tjeffree/Nova75-Keyboard/marbastlib-main/3d/CON_SM13B-SRSS-TB.step

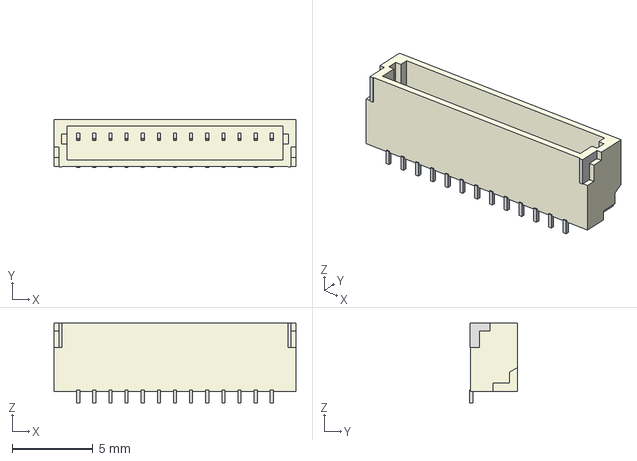
[picture p22: CAD file, 2022-10-29]
marbastlib-main/3d/CON_SM13B-SRSS-TB.step
15.0 x 2.96 x 4.95 mm
