tjeffree/Nova75-Keyboard/marbastlib-main/3d/LED_WS2812B-MINI.step

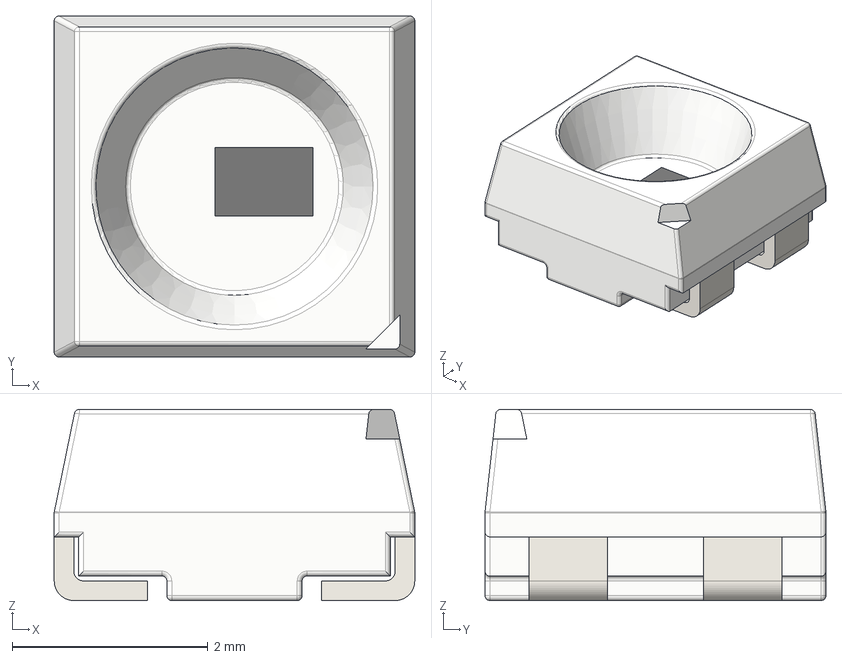
[picture p23: CAD file, 2022-10-29]
marbastlib-main/3d/LED_WS2812B-MINI.step
3.68 x 3.48 x 1.95 mm
