tjeffree/Nova75-Keyboard/marbastlib-main/3d/CON_SM08B-SRSS-TB.step

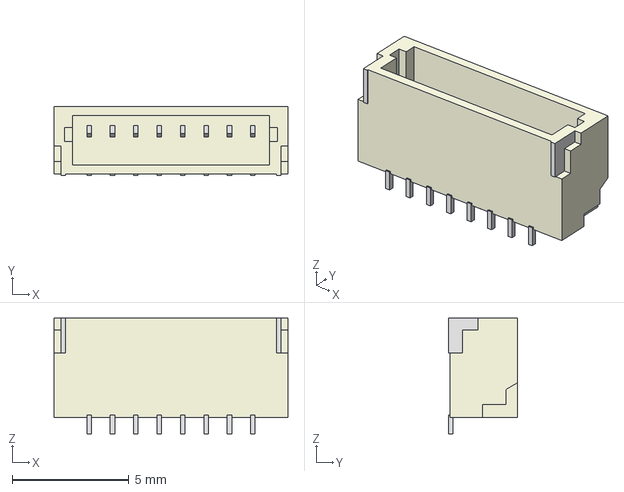
[picture p24: CAD file, 2022-10-29]
marbastlib-main/3d/CON_SM08B-SRSS-TB.step
10.0 x 2.96 x 4.95 mm
