tjeffree/Nova75-Keyboard/marbastlib-main/3d/SW_SSSS223900.step

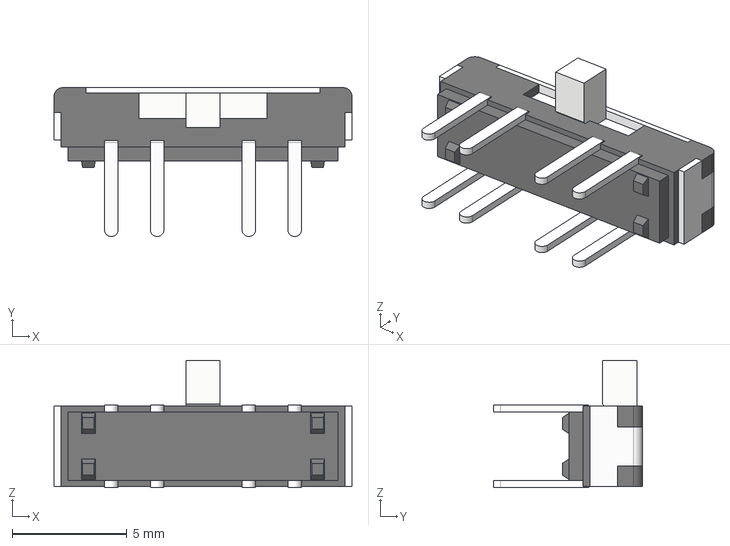
[picture p25: CAD file, 2022-10-29]
marbastlib-main/3d/SW_SSSS223900.step
13.0 x 6.50 x 5.55 mm
