tjeffree/Nova75-Keyboard/marbastlib-main/3d/CON_SM06B-SRSS-TB.step

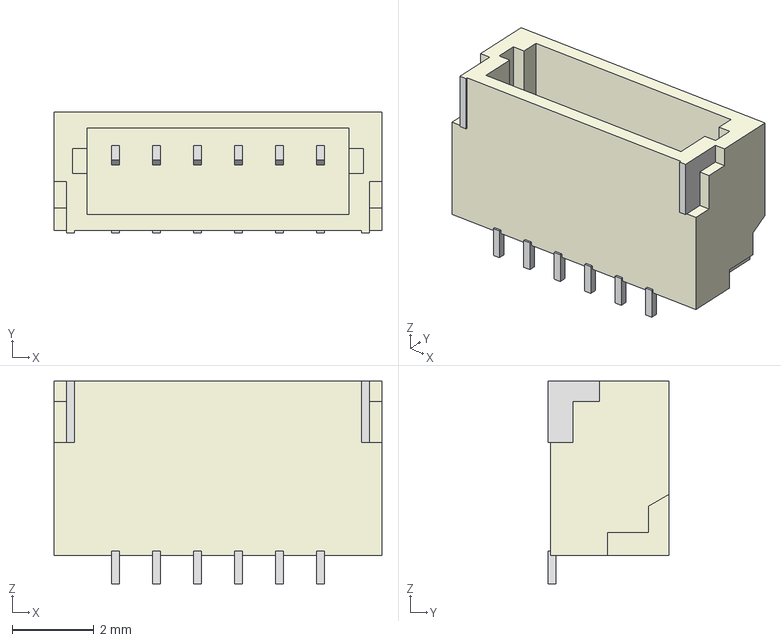
[picture p26: CAD file, 2022-10-29]
marbastlib-main/3d/CON_SM06B-SRSS-TB.step
8.00 x 2.96 x 4.95 mm
