tjeffree/Nova75-Keyboard/marbastlib-main/3d/Switch_MSK12C02.step

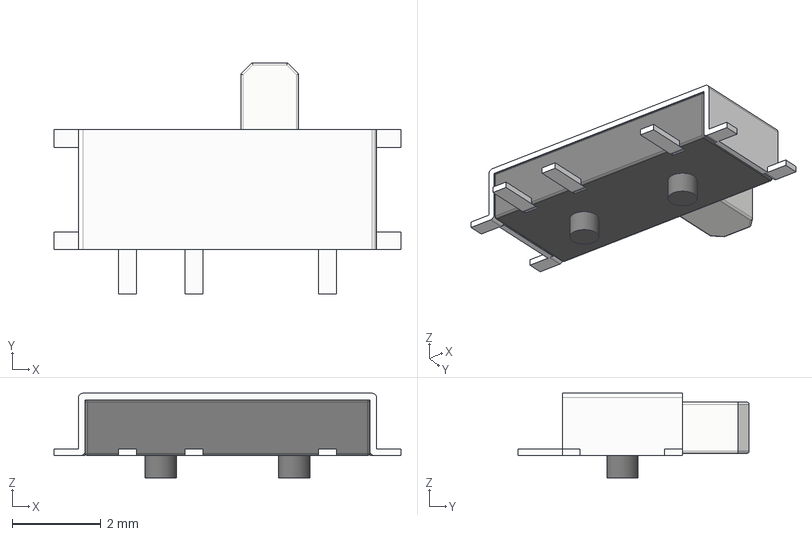
[picture p27: CAD file, 2022-10-29]
marbastlib-main/3d/Switch_MSK12C02.step
7.80 x 5.20 x 1.90 mm
