tjeffree/Nova75-Keyboard/marbastlib-main/3d/LED_WS2812_2020.step

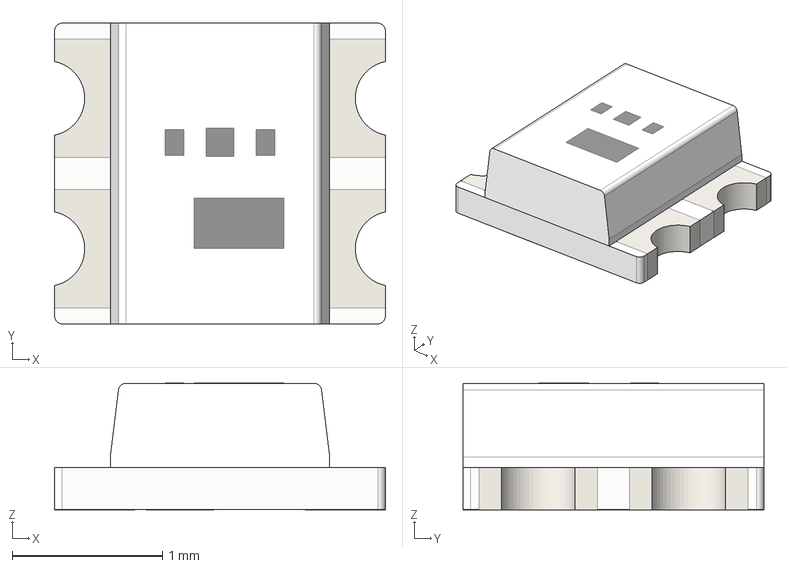
[picture p28: CAD file, 2022-10-29]
marbastlib-main/3d/LED_WS2812_2020.step
2.20 x 2.00 x 0.842 mm
