tjeffree/Nova75-Keyboard/marbastlib-main/3d/ROT_EC11E.step

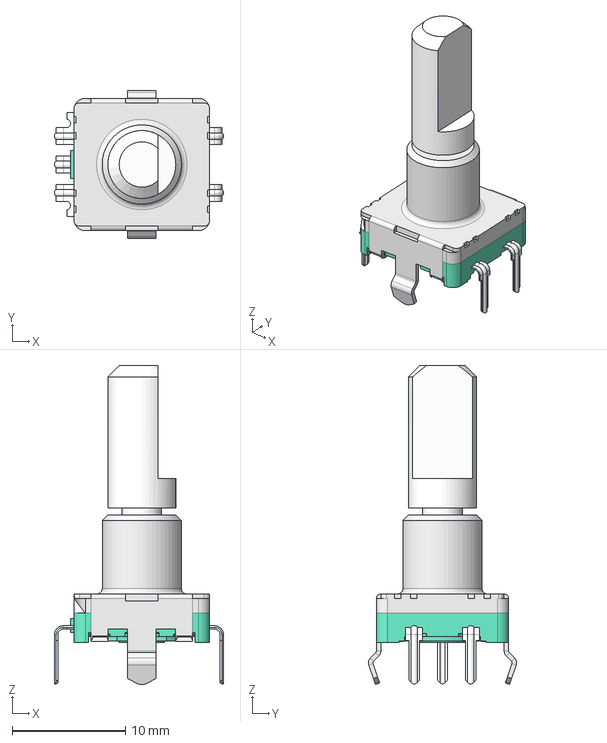
[picture p29: CAD file, 2022-10-29]
marbastlib-main/3d/ROT_EC11E.step
14.9 x 13.1 x 28.2 mm
