tjeffree/Nova75-Keyboard/marbastlib-main/3d/SW_SSSS213100.step

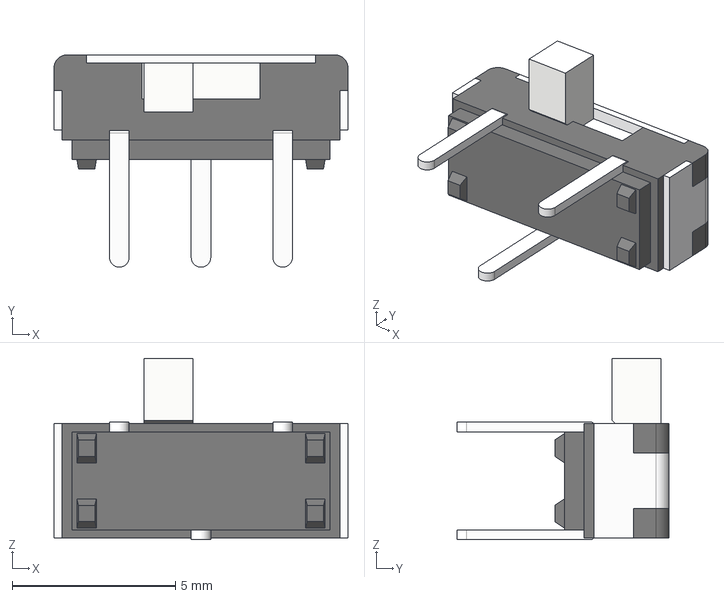
[picture p30: CAD file, 2022-10-29]
marbastlib-main/3d/SW_SSSS213100.step
9.00 x 6.50 x 5.55 mm
