tjeffree/Nova75-Keyboard/marbastlib-main/3d/CON_TYPE-C-31-M-14.step

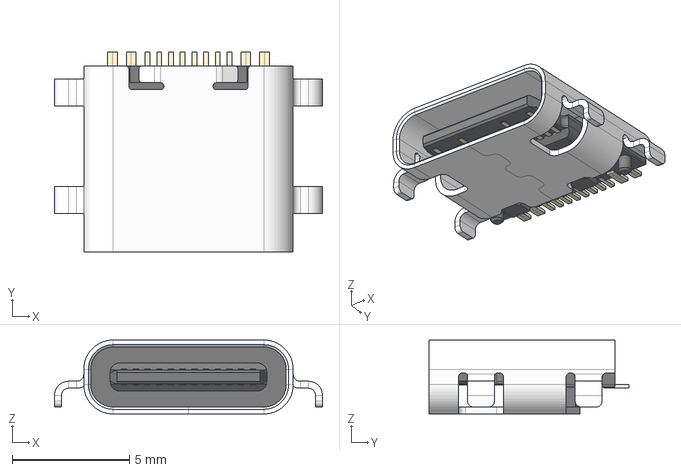
[picture p31: CAD file, 2022-10-29]
marbastlib-main/3d/CON_TYPE-C-31-M-14.step
11.5 x 8.56 x 3.16 mm
Shroud
Plastic Body & Connector
