tjeffree/Nova75-Keyboard/marbastlib-main/3d/Switch_ESP3020.step

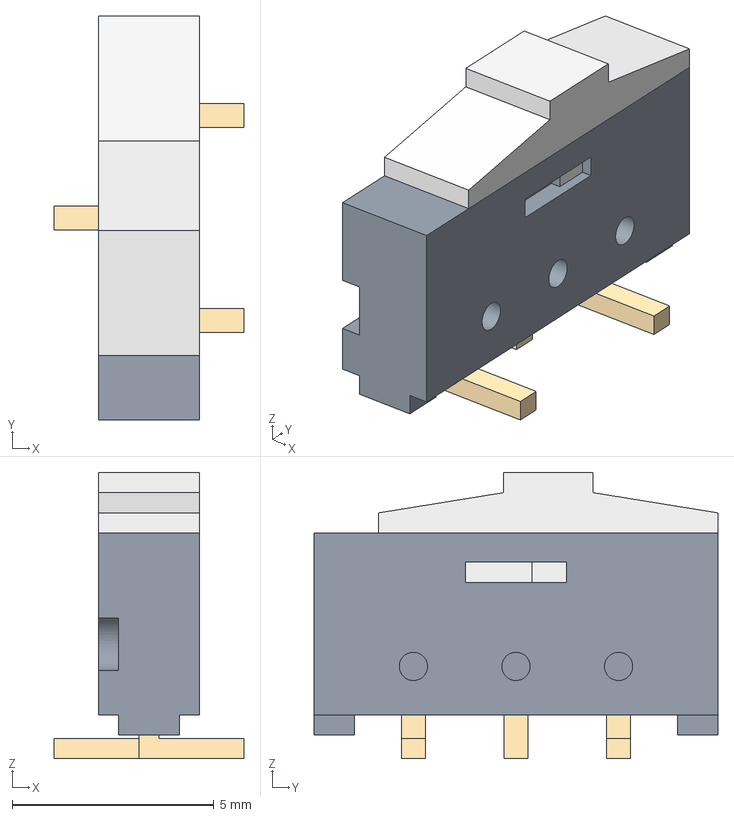
[picture p32: CAD file, 2022-10-29]
marbastlib-main/3d/Switch_ESP3020.step
4.70 x 10.0 x 7.08 mm
