tjeffree/Nova75-Keyboard/marbastlib-main/3d/CON_SM07B-SRSS-TB.step

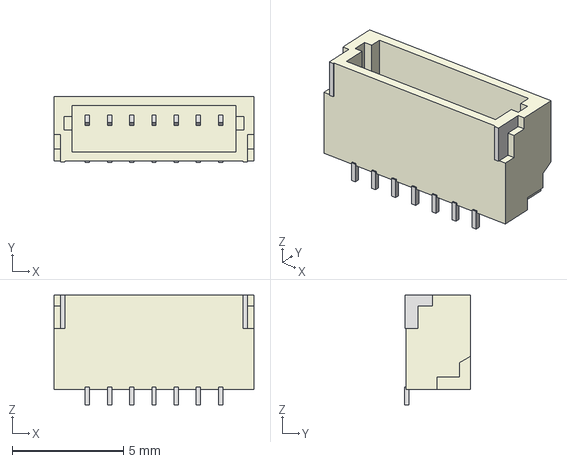
[picture p33: CAD file, 2022-10-29]
marbastlib-main/3d/CON_SM07B-SRSS-TB.step
9.00 x 2.96 x 4.95 mm
