tjeffree/Nova75-Keyboard/marbastlib-main/3d/Switch_SKQG.step

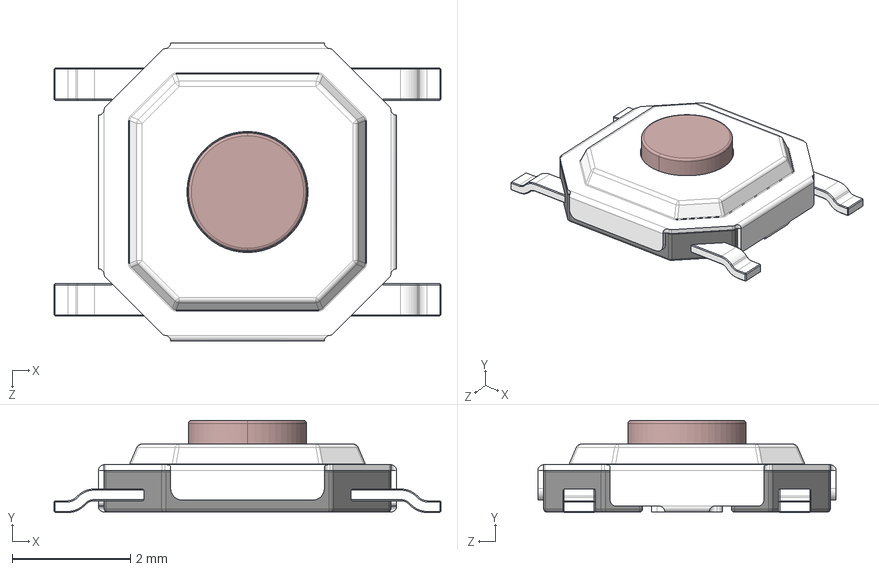
[picture p34: CAD file, 2022-10-29]
marbastlib-main/3d/Switch_SKQG.step
6.55 x 1.56 x 5.05 mm
bottom part_ﾄｬﾈﾏｨｨ_
bottom pin_ﾄｬﾈﾏｨｨ_
top shield_ﾄｬﾈﾏｨｨ_
copper button_ﾄｬﾈﾏｨｨ_
shrapnel_默认è_
