tjeffree/Nova75-Keyboard/marbastlib-main/3d/holyiot_18010_nRF52840.step

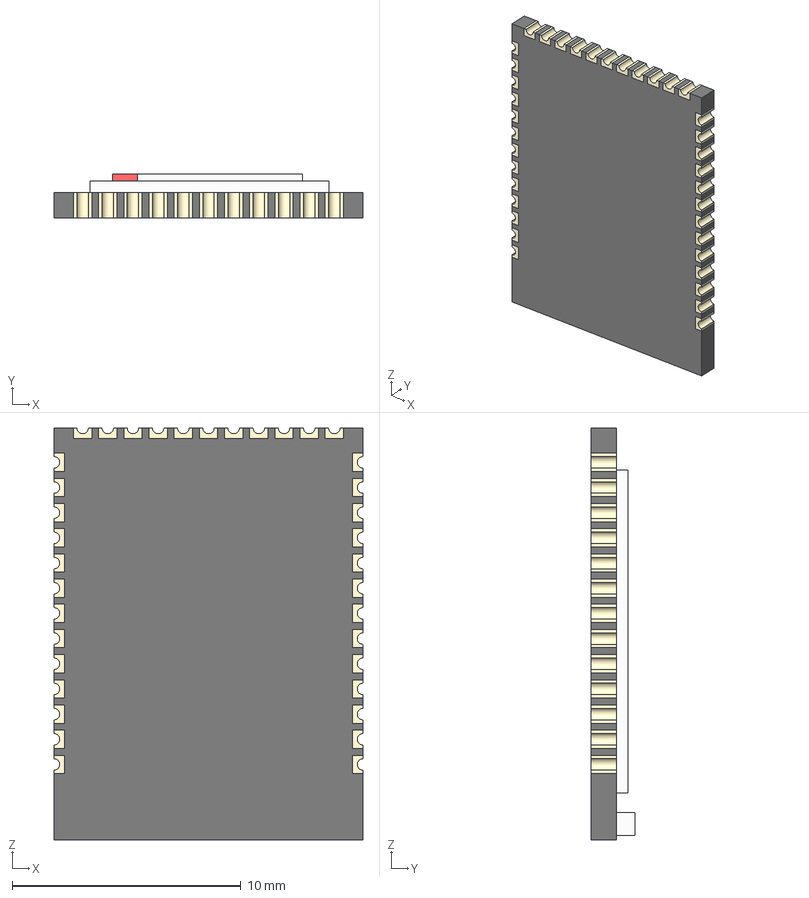
[picture p35: CAD file, 2022-10-29]
marbastlib-main/3d/holyiot_18010_nRF52840.step
13.5 x 1.92 x 18.0 mm
