tjeffree/Nova75-Keyboard/marbastlib-main/3d/joystick_psp1000.step

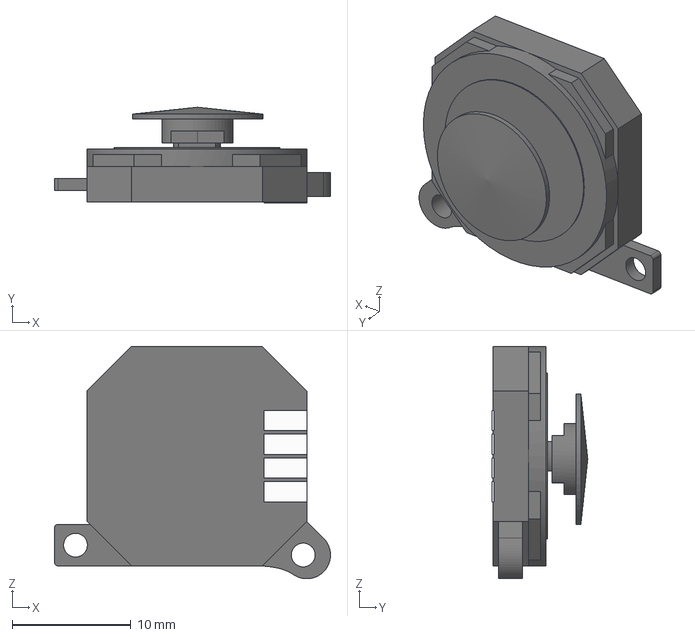
[picture p36: CAD file, 2022-10-29]
marbastlib-main/3d/joystick_psp1000.step
23.2 x 8.05 x 19.6 mm
