tjeffree/Nova75-Keyboard/marbastlib-main/3d/ROT_EC11N.step

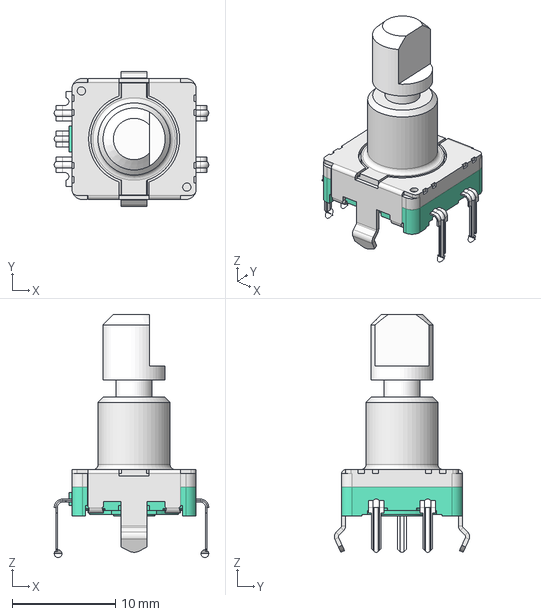
[picture p37: CAD file, 2022-10-29]
marbastlib-main/3d/ROT_EC11N.step
14.9 x 13.1 x 23.5 mm
