tjeffree/Nova75-Keyboard/marbastlib-main/3d/HS_Kailh_Choc.step

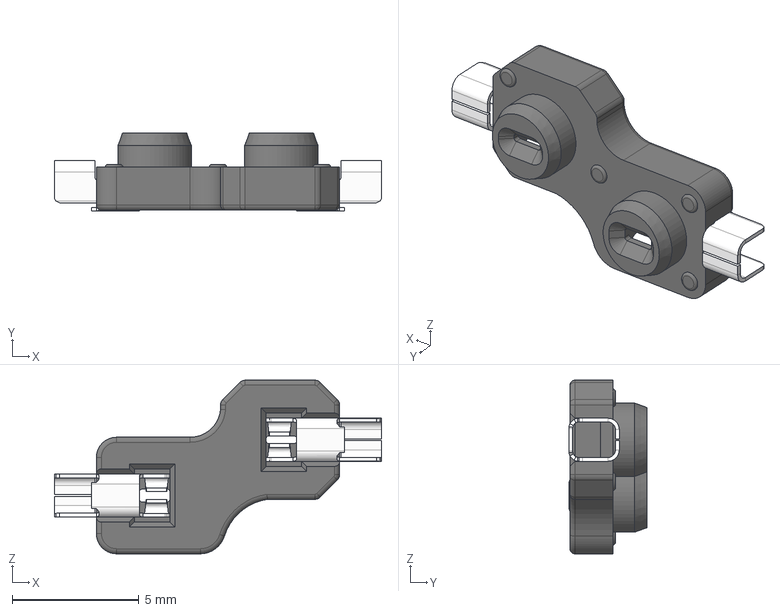
[picture p38: CAD file, 2022-10-29]
marbastlib-main/3d/HS_Kailh_Choc.step
12.9 x 3.09 x 6.85 mm
pin x 2
socket
