tjeffree/Nova75-Keyboard/marbastlib-main/3d/CON_TYPE-C-31-M-12.step

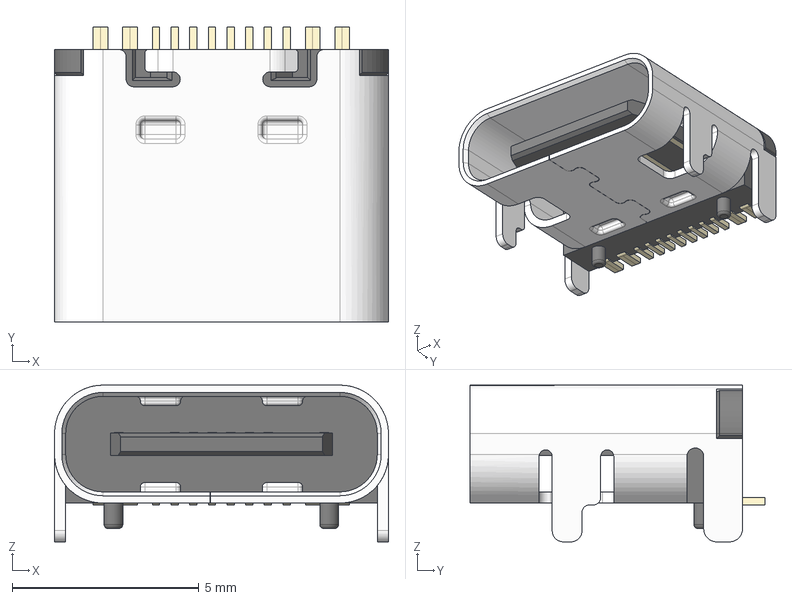
[picture p39: CAD file, 2022-10-29]
marbastlib-main/3d/CON_TYPE-C-31-M-12.step
8.95 x 7.90 x 4.20 mm
ConPins
PcbPins
Mold
Frame
