tjeffree/Nova75-Keyboard/marbastlib-main/3d/HS_Kailh_MX.step

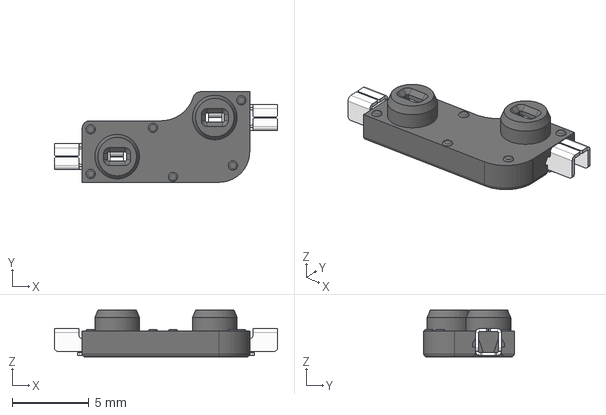
[picture p40: CAD file, 2022-10-29]
marbastlib-main/3d/HS_Kailh_MX.step
14.5 x 5.89 x 3.05 mm
Contact x 2
