tjeffree/Nova75-Keyboard/marbastlib-main/3d/CON_SM04B-SRSS-TB.step

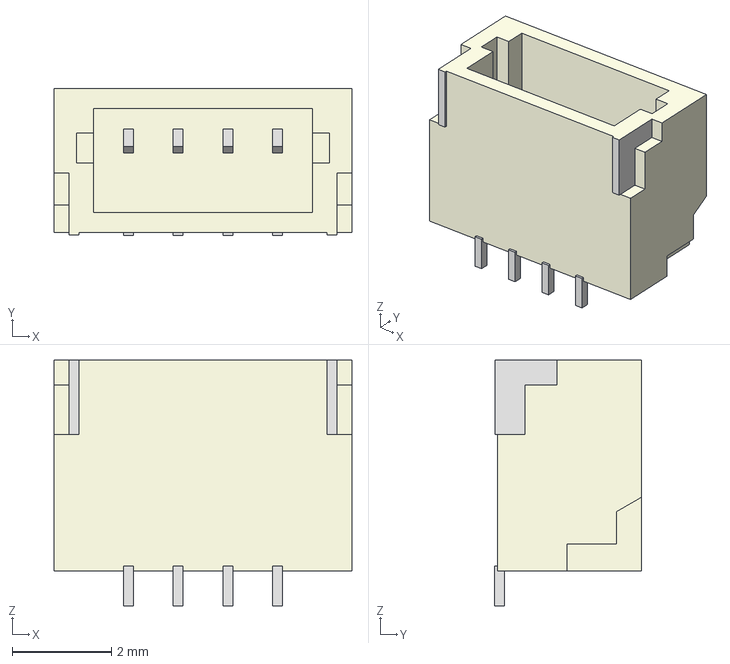
[picture p41: CAD file, 2022-10-29]
marbastlib-main/3d/CON_SM04B-SRSS-TB.step
6.00 x 2.96 x 4.95 mm
