tjeffree/Nova75-Keyboard/nova75.kicad_sch

## KiCad design nova75.kicad_sch (2022-11-14)

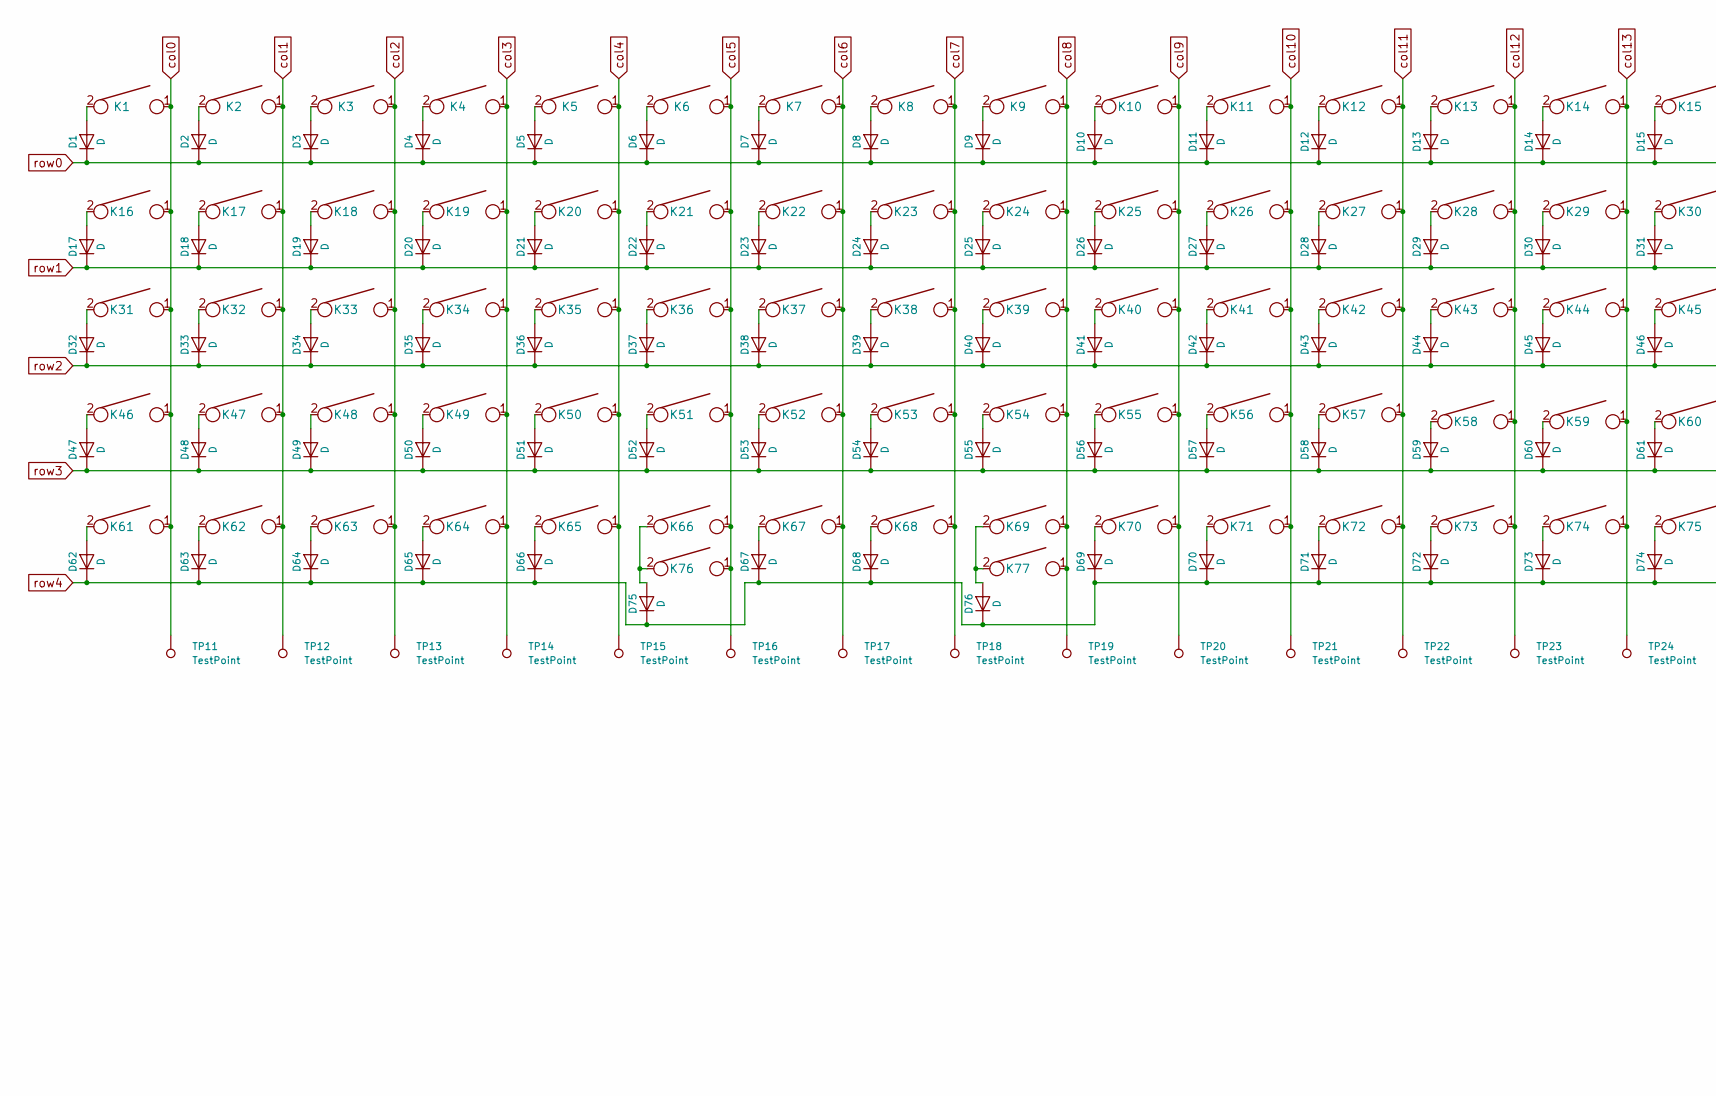
[picture p42: schematic nova75.kicad_sch, part in row 1, column 1]

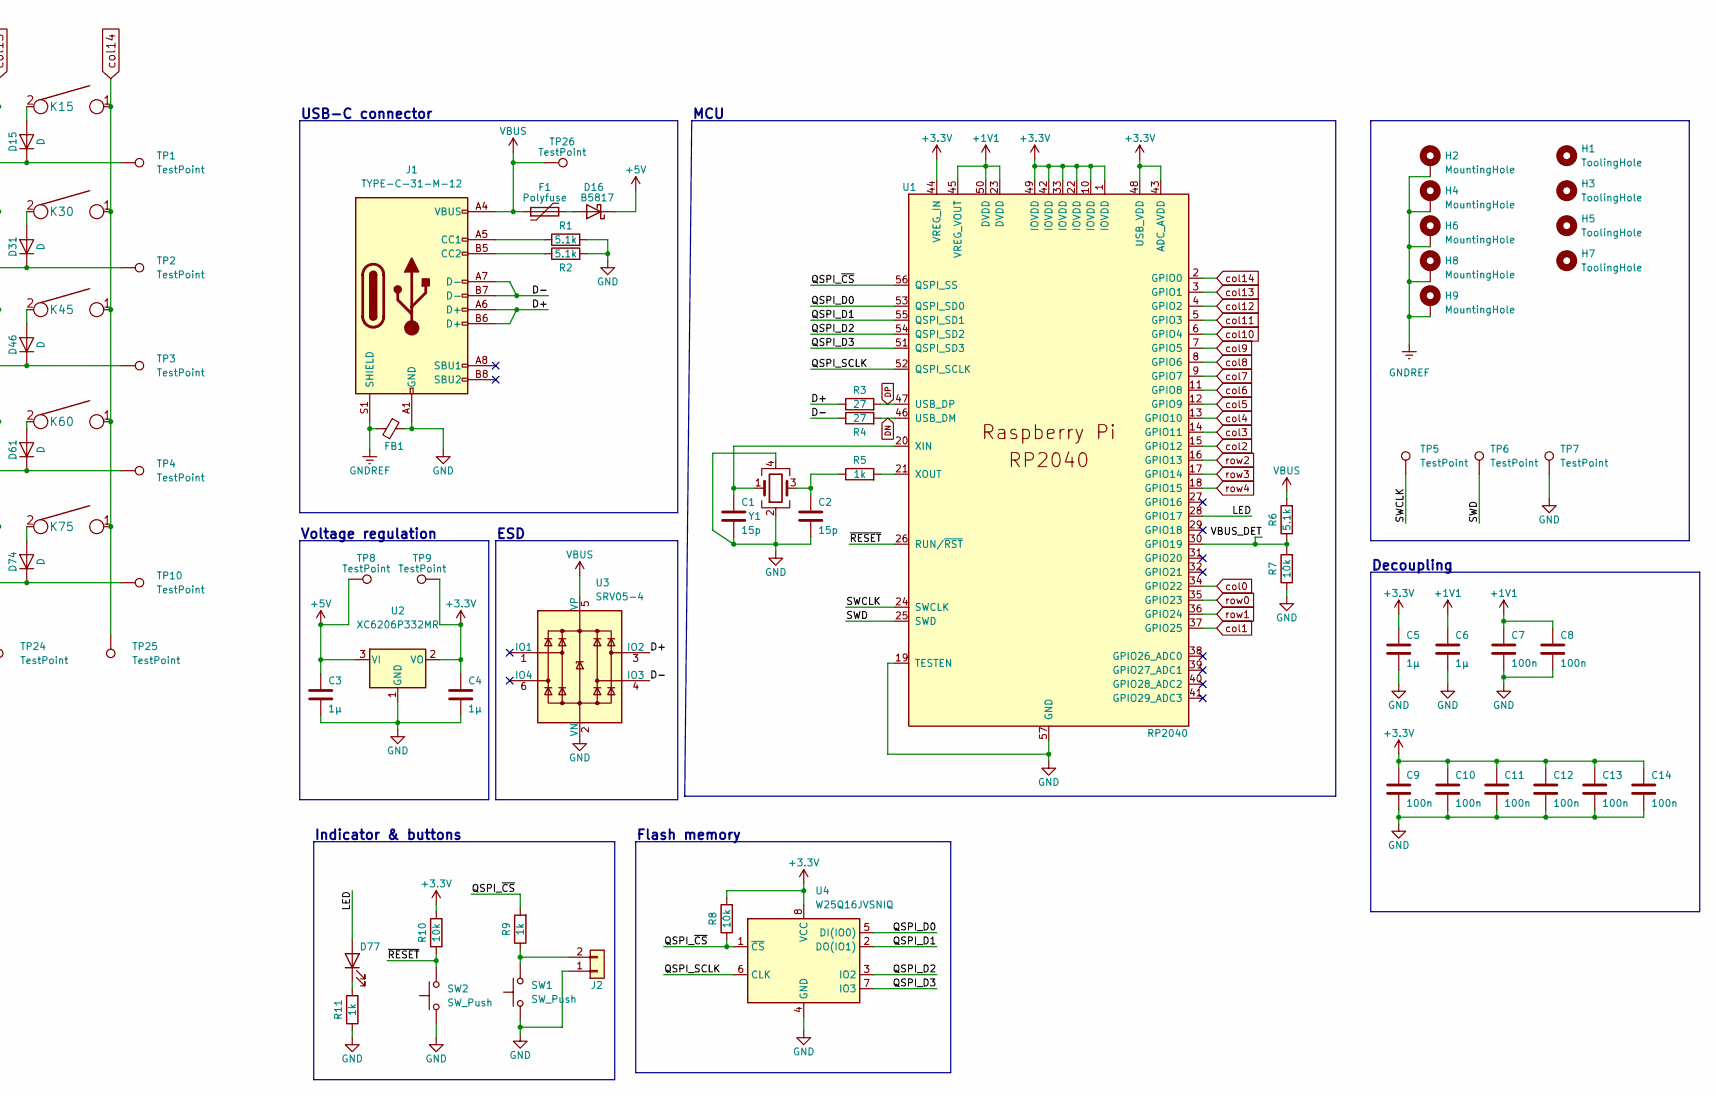
[picture p43: schematic nova75.kicad_sch, part in row 1, column 2]

Parts:
C1, C2: 15p; C_0402_1005Metric; LCSC C1548
C3, C4: 1µ; C_0603_1608Metric; LCSC C19666
C5, C6: 1µ; C_0402_1005Metric; LCSC C52923
C7, C8, C9, C10, C11, C12, C13, C14: 100n; C_0402_1005Metric; LCSC C1525
D1, D2, D3, D4, D5, D6, D7, D8, D9, D10, D11, D12, D13, D14, D15, D17, D18, D19, D20, D21, D22, D23, D24, D25, D26, D27, D28, D29, D30, D31, D32, D33, D34, D35, D36, D37, D38, D39, D40, D41, D42, D43, D44, D45, D46, D47, D48, D49, D50, D51, D52, D53, D54, D55, D56, D57, D58, D59, D60, D61, D62, D63, D64, D65, D66, D67, D68, D69, D70, D71, D72, D73, D74, D75, D76: D; D_SOD-123
D16: B5817; D_SOD-323; LCSC C123899
D77: LED; LED_0402_1005Metric; LCSC C130719
F1: Polyfuse; Fuse_0603_1608Metric; LCSC C69679
FB1: FerriteBead_Small; L_0603_1608Metric; LCSC C98288
H1, H3, H5, H7: ToolingHole; Tooling-Hole
H2, H4, H6, H8, H9: MountingHole; MountingHole_2.2mm_M2_elongated
J1: TYPE-C-31-M-12; USB_C_Receptacle_HRO_TYPE-C-31-M-12; LCSC C2848619
J2: Conn_01x02; PinHeader_1x02_P1.27mm_Vertical
K1, K2, K3, K4, K5, K6, K7, K8, K9, K10, K11, K12, K13, K14, K15, K16, K17, K18, K19, K20, K21, K22, K23, K24, K25, K26, K27, K28, K29, K30, K31, K32, K33, K34, K35, K36, K37, K38, K39, K40, K41, K42, K43, K44, K45, K46, K47, K48, K49, K50, K51, K52, K53, K54, K55, K56, K57, K58, K59, K60, K61, K62, K63, K64, K65, K67, K68, K70, K71, K72, K73, K74, K75, K76, K77: KEYSW; MXOnly-1U-Hotswap
K66, K69: KEYSW; MXOnly-2U-Hotswap-ReversedStabilizers
R1, R2, R6: 5.1k; R_0402_1005Metric; LCSC C25905
R3, R4: 27; R_0402_1005Metric; LCSC C25100
R5, R9, R11: 1k; R_0402_1005Metric; LCSC C11702
R7, R8, R10: 10k; R_0402_1005Metric; LCSC C25744
SW1, SW2: SW_Push; SW_SPST_CK_KXT3; LCSC C319433
TP1, TP2, TP3, TP4, TP10, TP11, TP12, TP13, TP14, TP15, TP16, TP17, TP18, TP19, TP20, TP21, TP22, TP23, TP24, TP25: TestPoint; TestPoint_Pad_D1.5mm
TP5, TP6, TP7: TestPoint; TestPoint_THTPad_1.5x1.5mm_Drill0.7mm
TP8, TP9, TP26: TestPoint; TestPoint_THTPad_D1.0mm_Drill0.5mm
U1: RP2040; QFN-56-1EP_7x7mm_P0.4mm_EP3.2x3.2mm; LCSC C2040
U2: XC6206P332MR; SOT-23; LCSC C82942
U3: SRV05-4; SOT-23-6-routable
U4: W25Q16JVSNIQ; SO-8_3.9x4.9mm_P1.27mm; LCSC C395484
Y1: Crystal_GND24; Crystal_SMD_2520-4Pin_2.5x2.0mm; LCSC C2149204

Connections:
+1V1: C6.1, C7.1, C8.1, U1.23 (DVDD), U1.45 (VREG_VOUT), U1.50 (DVDD)
+3.3V: C4.1, C5.1, C9.1, C10.1, C11.1, C12.1, C13.1, C14.1, R8.2, R10.2, TP9.1, U1.1 (IOVDD), U1.10 (IOVDD), U1.22 (IOVDD), U1.33 (IOVDD), U1.42 (IOVDD), U1.43 (ADC_AVDD), U1.44 (VREG_IN), U1.48 (USB_VDD), U1.49 (IOVDD), U2.2 (VO), U4.8 (VCC)
+5V: C3.1, D16.1 (K), TP8.1, U2.3 (VI)
D+: J1.A6 (D+), J1.B6 (D+), R3.1, U3.3 (IO2)
D-: J1.A7 (D-), J1.B7 (D-), R4.1, U3.4 (IO3)
DN: R4.2, U1.46 (USB_DM)
DP: R3.2, U1.47 (USB_DP)
GND: C1.2, C2.2, C3.2, C4.2, C5.2, C6.2, C7.2, C8.2, C9.2, C10.2, C11.2, C12.2, C13.2, C14.2, FB1.1, J1.A1 (GND), J1.A12 (GND), J1.B1 (GND), J1.B12 (GND), J2.1, R1.2, R2.2, R7.1, R11.1, SW1.1, SW2.1, TP7.1, U1.19 (TESTEN), U1.57 (GND), U2.1 (GND), U3.2 (VN), U4.4 (GND), Y1.2, Y1.4
GNDREF: FB1.2, H2.1, H4.1, H6.1, H8.1, H9.1, J1.S1 (SHIELD)
LED: D77.2 (A), U1.28 (GPIO17)
unnamed: C1.1, U1.20 (XIN), Y1.1
unnamed: C2.1, R5.1, Y1.3
unnamed: D1.2 (A), K1.2
unnamed: D2.2 (A), K2.2
unnamed: D3.2 (A), K3.2
unnamed: D4.2 (A), K4.2
unnamed: D5.2 (A), K5.2
unnamed: D6.2 (A), K6.2
unnamed: D7.2 (A), K7.2
unnamed: D8.2 (A), K8.2
unnamed: D9.2 (A), K9.2
unnamed: D10.2 (A), K10.2
unnamed: D11.2 (A), K11.2
unnamed: D12.2 (A), K12.2
unnamed: D13.2 (A), K13.2
unnamed: D14.2 (A), K14.2
unnamed: D15.2 (A), K15.2
unnamed: D16.2 (A), F1.2
unnamed: D17.2 (A), K16.2
unnamed: D18.2 (A), K17.2
unnamed: D19.2 (A), K18.2
unnamed: D20.2 (A), K19.2
unnamed: D21.2 (A), K20.2
unnamed: D22.2 (A), K21.2
unnamed: D23.2 (A), K22.2
unnamed: D24.2 (A), K23.2
unnamed: D25.2 (A), K24.2
unnamed: D26.2 (A), K25.2
unnamed: D27.2 (A), K26.2
unnamed: D28.2 (A), K27.2
unnamed: D29.2 (A), K28.2
unnamed: D30.2 (A), K29.2
unnamed: D31.2 (A), K30.2
unnamed: D32.2 (A), K31.2
unnamed: D33.2 (A), K32.2
unnamed: D34.2 (A), K33.2
unnamed: D35.2 (A), K34.2
unnamed: D36.2 (A), K35.2
unnamed: D37.2 (A), K36.2
unnamed: D38.2 (A), K37.2
unnamed: D39.2 (A), K38.2
unnamed: D40.2 (A), K39.2
unnamed: D41.2 (A), K40.2
unnamed: D42.2 (A), K41.2
unnamed: D43.2 (A), K42.2
unnamed: D44.2 (A), K43.2
unnamed: D45.2 (A), K44.2
unnamed: D46.2 (A), K45.2
unnamed: D47.2 (A), K46.2
unnamed: D48.2 (A), K47.2
unnamed: D49.2 (A), K48.2
unnamed: D50.2 (A), K49.2
unnamed: D51.2 (A), K50.2
unnamed: D52.2 (A), K51.2
unnamed: D53.2 (A), K52.2
unnamed: D54.2 (A), K53.2
unnamed: D55.2 (A), K54.2
unnamed: D56.2 (A), K55.2
unnamed: D57.2 (A), K56.2
unnamed: D58.2 (A), K57.2
unnamed: D59.2 (A), K58.2
unnamed: D60.2 (A), K59.2
unnamed: D61.2 (A), K60.2
unnamed: D62.2 (A), K61.2
unnamed: D63.2 (A), K62.2
unnamed: D64.2 (A), K63.2
unnamed: D65.2 (A), K64.2
unnamed: D66.2 (A), K65.2
unnamed: D67.2 (A), K67.2
unnamed: D68.2 (A), K68.2
unnamed: D69.2 (A), K70.2
unnamed: D70.2 (A), K71.2
unnamed: D71.2 (A), K72.2
unnamed: D72.2 (A), K73.2
unnamed: D73.2 (A), K74.2
unnamed: D74.2 (A), K75.2
unnamed: D75.2 (A), K66.2, K76.2
unnamed: D76.2 (A), K69.2, K77.2
unnamed: D77.1 (K), R11.2
unnamed: J1.A5 (CC1), R1.1
unnamed: J1.B5 (CC2), R2.1
unnamed: J2.2, R9.1, SW1.2
unnamed: R5.2, U1.21 (XOUT)
QSPI_D0: U1.53 (QSPI_SD0), U4.5 (DI(IO0))
QSPI_D1: U1.55 (QSPI_SD1), U4.2 (DO(IO1))
QSPI_D2: U1.54 (QSPI_SD2), U4.3 (IO2)
QSPI_D3: U1.51 (QSPI_SD3), U4.7 (IO3)
QSPI_SCLK: U1.52 (QSPI_SCLK), U4.6 (CLK)
QSPI_~CS: R8.1, R9.2, U1.56 (QSPI_SS), U4.1 (~CS)
SWCLK: TP5.1, U1.24 (SWCLK)
SWD: TP6.1, U1.25 (SWD)
VBUS: F1.1, J1.A4 (VBUS), J1.A9 (VBUS), J1.B4 (VBUS), J1.B9 (VBUS), R6.2, TP26.1, U3.5 (VP)
VBUS_DET: R6.1, R7.2, U1.30 (GPIO19)
col0: K1.1, K16.1, K31.1, K46.1, K61.1, TP11.1, U1.34 (GPIO22)
col1: K2.1, K17.1, K32.1, K47.1, K62.1, TP12.1, U1.37 (GPIO25)
col2: K3.1, K18.1, K33.1, K48.1, K63.1, TP13.1, U1.15 (GPIO12)
col3: K4.1, K19.1, K34.1, K49.1, K64.1, TP14.1, U1.14 (GPIO11)
col4: K5.1, K20.1, K35.1, K50.1, K65.1, TP15.1, U1.13 (GPIO10)
col5: K6.1, K21.1, K36.1, K51.1, K66.1, K76.1, TP16.1, U1.12 (GPIO9)
col6: K7.1, K22.1, K37.1, K52.1, K67.1, TP17.1, U1.11 (GPIO8)
col7: K8.1, K23.1, K38.1, K53.1, K68.1, TP18.1, U1.9 (GPIO7)
col8: K9.1, K24.1, K39.1, K54.1, K69.1, K77.1, TP19.1, U1.8 (GPIO6)
col9: K10.1, K25.1, K40.1, K55.1, K70.1, TP20.1, U1.7 (GPIO5)
col10: K11.1, K26.1, K41.1, K56.1, K71.1, TP21.1, U1.6 (GPIO4)
col11: K12.1, K27.1, K42.1, K57.1, K72.1, TP22.1, U1.5 (GPIO3)
col12: K13.1, K28.1, K43.1, K58.1, K73.1, TP23.1, U1.4 (GPIO2)
col13: K14.1, K29.1, K44.1, K59.1, K74.1, TP24.1, U1.3 (GPIO1)
col14: K15.1, K30.1, K45.1, K60.1, K75.1, TP25.1, U1.2 (GPIO0)
row0: D1.1 (K), D2.1 (K), D3.1 (K), D4.1 (K), D5.1 (K), D6.1 (K), D7.1 (K), D8.1 (K), D9.1 (K), D10.1 (K), D11.1 (K), D12.1 (K), D13.1 (K), D14.1 (K), D15.1 (K), TP1.1, U1.35 (GPIO23)
row1: D17.1 (K), D18.1 (K), D19.1 (K), D20.1 (K), D21.1 (K), D22.1 (K), D23.1 (K), D24.1 (K), D25.1 (K), D26.1 (K), D27.1 (K), D28.1 (K), D29.1 (K), D30.1 (K), D31.1 (K), TP2.1, U1.36 (GPIO24)
row2: D32.1 (K), D33.1 (K), D34.1 (K), D35.1 (K), D36.1 (K), D37.1 (K), D38.1 (K), D39.1 (K), D40.1 (K), D41.1 (K), D42.1 (K), D43.1 (K), D44.1 (K), D45.1 (K), D46.1 (K), TP3.1, U1.16 (GPIO13)
row3: D47.1 (K), D48.1 (K), D49.1 (K), D50.1 (K), D51.1 (K), D52.1 (K), D53.1 (K), D54.1 (K), D55.1 (K), D56.1 (K), D57.1 (K), D58.1 (K), D59.1 (K), D60.1 (K), D61.1 (K), TP4.1, U1.17 (GPIO14)
row4: D62.1 (K), D63.1 (K), D64.1 (K), D65.1 (K), D66.1 (K), D67.1 (K), D68.1 (K), D69.1 (K), D70.1 (K), D71.1 (K), D72.1 (K), D73.1 (K), D74.1 (K), D75.1 (K), D76.1 (K), TP10.1, U1.18 (GPIO15)
~RESET: R10.1, SW2.2, U1.26 (RUN/~RST)

Notes on the sheet:
Flash memory
ESD
Decoupling
Voltage regulation
MCU
USB-C connector
Indicator & buttons
